sparkfunX/SparkX_smol_Power_Board_AAA/Firmware/smol_Power_Board/smol_Power_Board_Constants.h

// smôl Power Board EEPROM constants

//Define the firmware version
#define SMOL_POWER_BOARD_FIRMWARE_VERSION    0x10 // v1.0

//Define the ATtiny43's default I2C address
#define SMOL_POWER_DEFAULT_I2C_ADDRESS                 0x50

//Define the WDT prescaler settings
#define SFE_SMOL_POWER_WDT_TIMEOUT_16ms            0x00 // 16ms timeout
#define SFE_SMOL_POWER_WDT_TIMEOUT_32ms            0x01 // 32ms timeout
#define SFE_SMOL_POWER_WDT_TIMEOUT_64ms            0x02 // 64ms timeout
#define SFE_SMOL_POWER_WDT_TIMEOUT_125ms           0x03 // 0.125s timeout
#define SFE_SMOL_POWER_WDT_TIMEOUT_250ms           0x04 // 0.25s timeout
#define SFE_SMOL_POWER_WDT_TIMEOUT_500ms           0x05 // 0.5s timeout
#define SFE_SMOL_POWER_WDT_TIMEOUT_1s              0x06 // 1.0s timeout
#define SFE_SMOL_POWER_WDT_TIMEOUT_2s              0x07 // 2.0s timeout
#define SFE_SMOL_POWER_WDT_TIMEOUT_4s              0x08 // 4.0s timeout
#define SFE_SMOL_POWER_WDT_TIMEOUT_8s              0x09 // 8.0s timeout
#define SMOL_POWER_DEFAULT_WDT_PRESCALER SFE_SMOL_POWER_WDT_TIMEOUT_1s

//Define the firmware register addresses:
#define SFE_SMOL_POWER_REGISTER_I2C_ADDRESS        0x00 // byte     Read/Write: Stored in eeprom
#define SFE_SMOL_POWER_REGISTER_RESET_REASON       0x01 // byte     Read only
#define SFE_SMOL_POWER_REGISTER_TEMPERATURE        0x02 // uint16_t Read only
#define SFE_SMOL_POWER_REGISTER_VBAT               0x03 // uint16_t Read only
#define SFE_SMOL_POWER_REGISTER_1V1                0x04 // uint16_t Read only
#define SFE_SMOL_POWER_REGISTER_ADC_REFERENCE      0x05 // byte     Read/Write
#define SFE_SMOL_POWER_REGISTER_WDT_PRESCALER      0x06 // byte     Read/Write: Stored in eeprom
#define SFE_SMOL_POWER_REGISTER_POWERDOWN_DURATION 0x07 // uint16_t Read/Write: Stored in eeprom
#define SFE_SMOL_POWER_REGISTER_POWERDOWN_NOW      0x08 //          Write only (Sequence is: "SLEEP" + CRC)
#define SFE_SMOL_POWER_REGISTER_FIRMWARE_VERSION   0x09 // byte     Read only
#define SFE_SMOL_POWER_REGISTER_UNKNOWN            0xFF

//Reset Reason (MCUSR) Flags
#define SFE_SMOL_POWER_RESET_REASON_PORF_BIT       0                                           ///< Bit position of the Power-on Reset Flag
#define SFE_SMOL_POWER_RESET_REASON_PORF           (1 << SFE_SMOL_POWER_RESET_REASON_PORF_BIT)        ///< Flag to indicate if the MCUSR PORF Flag was set when the ATtiny43U came out of reset
#define SFE_SMOL_POWER_RESET_REASON_EXTRF_BIT      1                                           ///< Bit position of the External Reset Flag
#define SFE_SMOL_POWER_RESET_REASON_EXTRF          (1 << SFE_SMOL_POWER_RESET_REASON_EXTRF_BIT)       ///< Flag to indicate if the MCUSR EXTRF Flag was set when the ATtiny43U came out of reset
#define SFE_SMOL_POWER_RESET_REASON_BORF_BIT       2                                           ///< Bit position of the Brown-out Reset Flag
#define SFE_SMOL_POWER_RESET_REASON_BORF           (1 << SFE_SMOL_POWER_RESET_REASON_BORF_BIT)        ///< Flag to indicate if the MCUSR BORF Flag was set when the ATtiny43U came out of reset
#define SFE_SMOL_POWER_RESET_REASON_WDRF_BIT       3                                           ///< Bit position of the Watchdog Reset Flag
#define SFE_SMOL_POWER_RESET_REASON_WDRF           (1 << SFE_SMOL_POWER_RESET_REASON_WDRF_BIT)        ///< Flag to indicate if the MCUSR WDRF Flag was set when the ATtiny43U came out of reset
#define SFE_SMOL_POWER_EEPROM_CORRUPT_ON_RESET_BIT 4                                           ///< Bit position of the eeprom memory corrupt on reset flag
#define SFE_SMOL_POWER_EEPROM_CORRUPT_ON_RESET     (1 << SFE_SMOL_POWER_EEPROM_CORRUPT_ON_RESET_BIT)  ///< Flag to indicate if the ATtiny43U's eeprom memory was corrupt on reset and has been overwritten with the default settings

//ADC Reference
#define SFE_SMOL_POWER_ADC_REFERENCE_VCC           0
#define SFE_SMOL_POWER_ADC_REFERENCE_1V1           1
