sparkfunX/SparkX_smol_Power_Board_AAA/Firmware/smol_Power_Board/smol_Power_Board_EEPROM.h

// smôl Power Board EEPROM storage and functions

struct struct_eeprom_settings {
  byte sizeOfSettings = 0; //sizeOfSettings **must** be the first entry and must be byte
  byte firmwareVersion = SMOL_POWER_BOARD_FIRMWARE_VERSION; // firmwareVersion **must** be the second entry
  byte i2cAddress = SMOL_POWER_DEFAULT_I2C_ADDRESS;
  byte wdtPrescaler = SMOL_POWER_DEFAULT_WDT_PRESCALER;
  uint16_t powerDownDuration = 1; // Default to power-down of 1 WDT interrupt
  byte CRC;
} eeprom_settings;
