sparkfunX/SparkX_smol_Power_Board_AAA/Firmware/smol_Power_Board/smol_Power_Board_WDT.ino

// smôl Power Board WDT functions

// Based on https://electronics.stackexchange.com/questions/74840/use-avr-watchdog-like-normal-isr

// ISR for watchdog timer
ISR(WDT_vect) {
  sleep_disable(); // Clear the Sleep Enable (SE) bit in the MCUCR register
  // To avoid the Watchdog Reset, WDIE must be set after each interrupt.
  WDTCSR |= (1 << WDIE); // Re-enable the WDT interrupt. Don't disable the WDT. Don't change the prescaler.
  if (powerDownDuration > 0) // Decrement powerDownDuration
    powerDownDuration--;
  sleep_enable(); // Set the Sleep Enable (SE) bit in the MCUCR register so sleep is possible
}

// Disable the WDT
void disableWDT()
{
  cli(); // Disable interrupts
#ifdef POWER_BOARD_LIPO
  CCP = 0xD8; // Write signature (0xD8) to the Configuration Change Register
#else
  WDTCSR |= (1 << WDCE) | (1 << WDE); // In the same operation, write a logic one to WDCE and WDE
#endif
  // Within the next four clock cycles, write a logic 0 to WDE.
  WDTCSR = 0x00; // Disable the Watchdog and the interrupt and clear the prescaler.
  sei(); // Enable interrupts
}

// Enable the WDT:
// Enable both the Watchdog Timeout Interrupt (WDIE) _and_ the Watchdog itself (WDE)
// The WDT will generate an interrupt after a time-out of prescaler cycles
// The WDIE bit needs to be (re)set by the ISR to prevent the WDT from resetting the CPU at the next time-out
void enableWDT()
{
  cli(); // Disable interrupts
  // Make wdtBits volatile to avoid the compiled code for the "WDTCSR = wdtBits"
  //  being too slow and not meeting the "within four clock cycles" requirement.
  volatile byte wdtBits = (1 << WDIE) | (1 << WDE) | ((eeprom_settings.wdtPrescaler & 0x08) << 2)
                          | (eeprom_settings.wdtPrescaler & 0x07); // WDT Interrupt Enable OR'd with WDE and the four prescaler bits
#ifdef POWER_BOARD_LIPO
  CCP = 0xD8; // Write signature (0xD8) to the Configuration Change Register
#else
  WDTCSR |= (1 << WDCE) | (1 << WDE); // We need to set WDCE when changing the prescaler bits
#endif
  WDTCSR = wdtBits; // Enable the WDT interrupt, WDT and set the prescaler
  sei(); // Enable interrupts
}
